samlli/Split-65/images/bottom.png

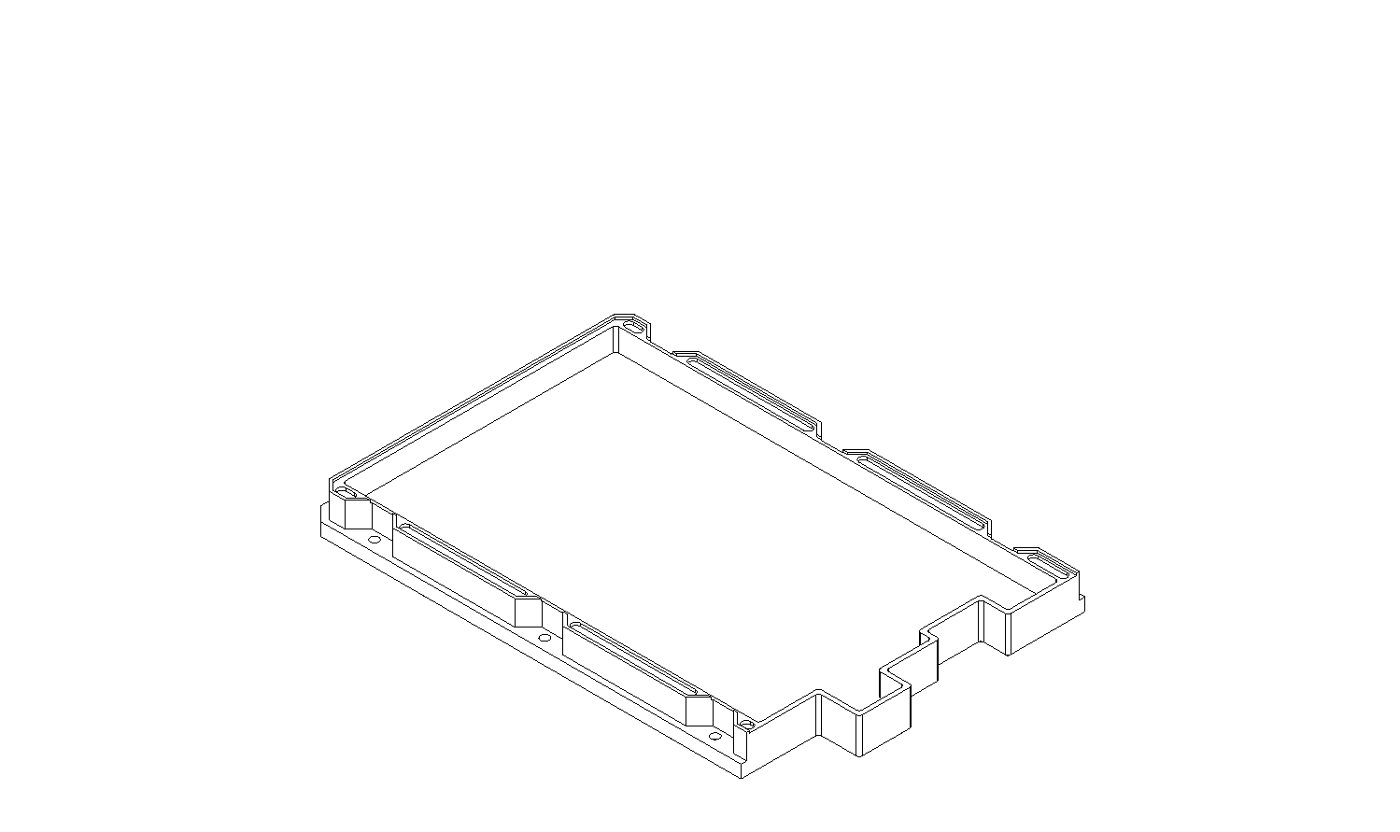
images/bottom.png
