samlli/Split-65/images/capture1.png

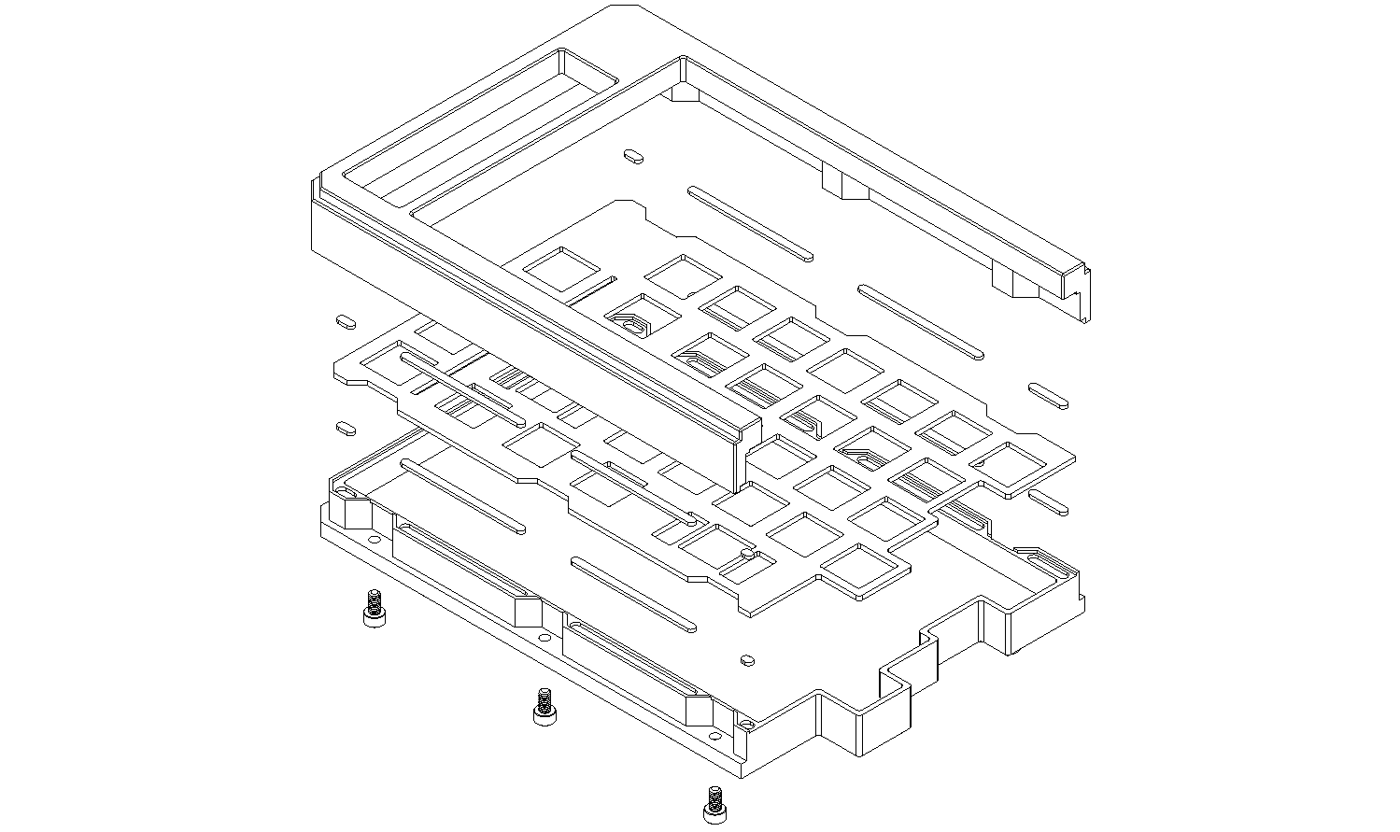
images/capture1.png
