samlli/Split-65/images/explodedview2.png

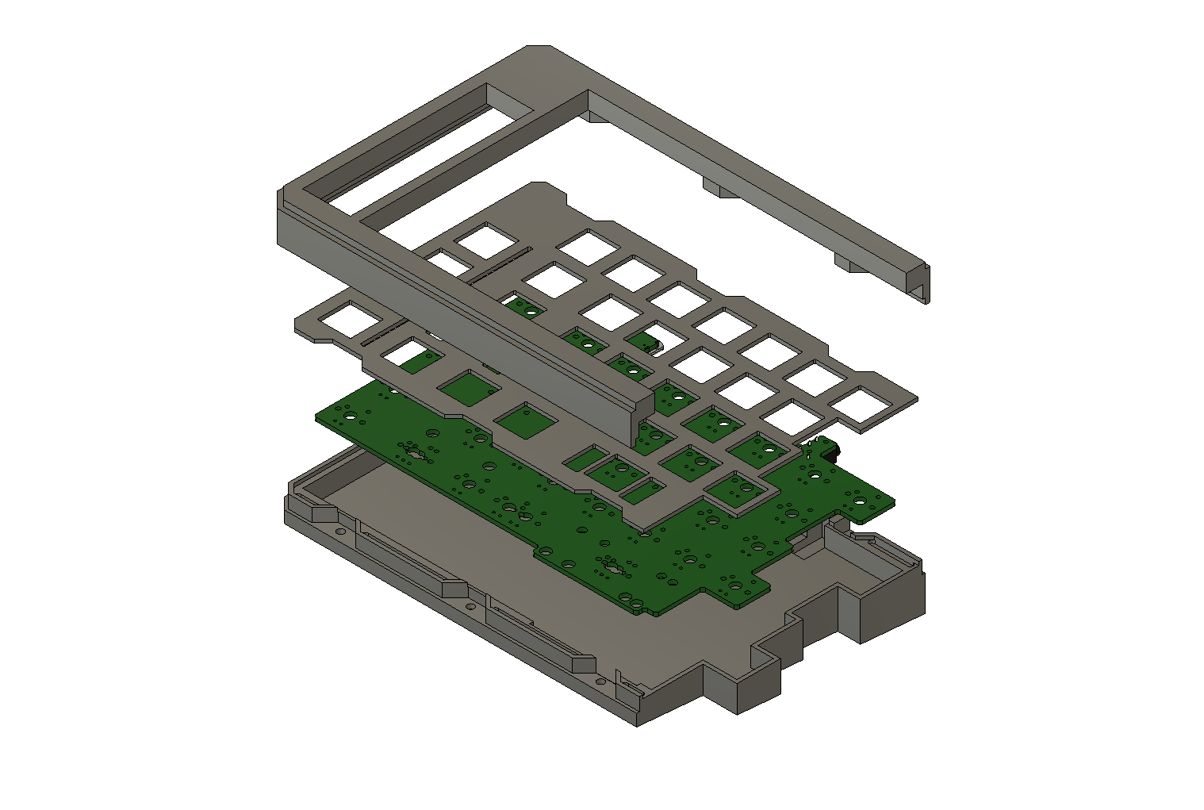
images/explodedview2.png
