samlli/Split-65/images/gasketbottom.png

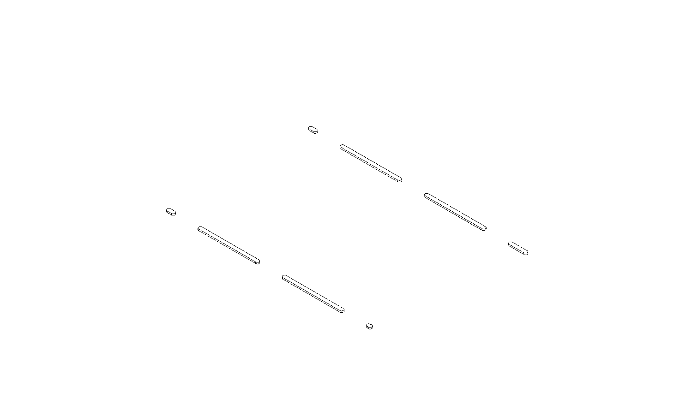
images/gasketbottom.png
