samlli/Split-65/images/gaskettop.png

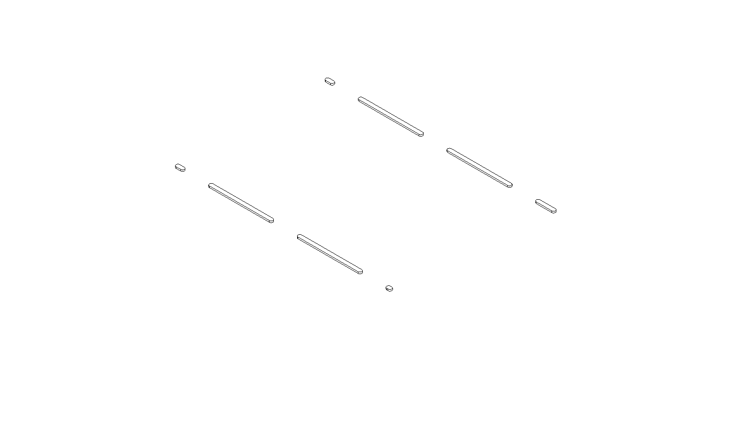
images/gaskettop.png
