samlli/Split-65/images/liverender1.png

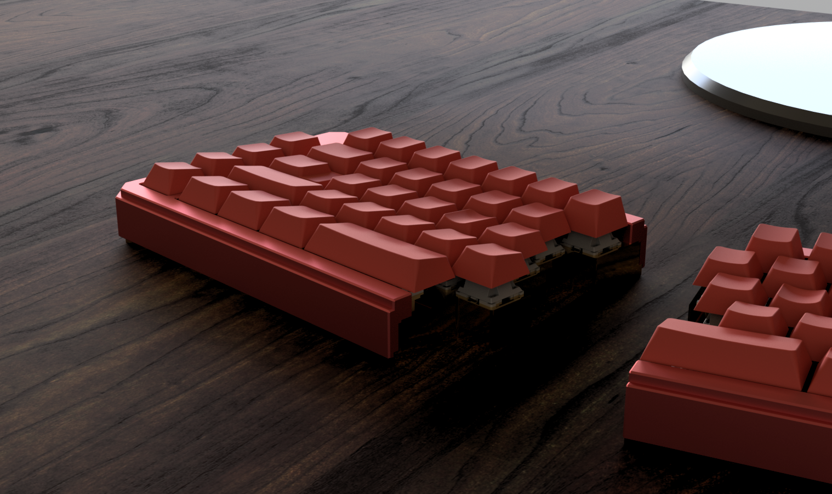
images/liverender1.png
