samlli/Split-65/images/myeyes.png

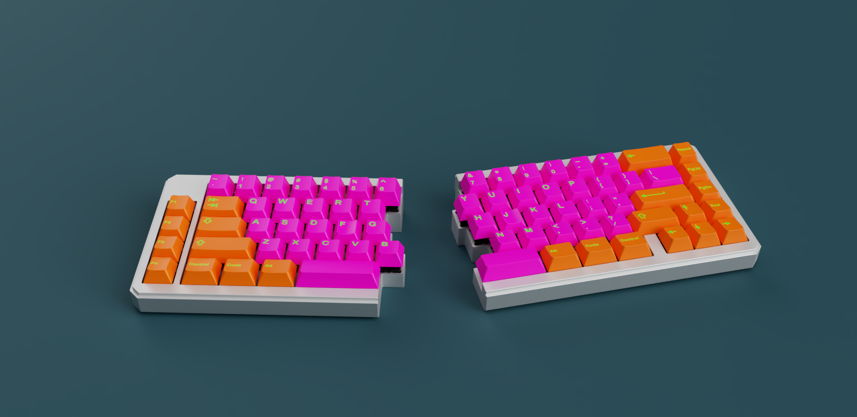
images/myeyes.png
