samlli/Split-65/images/plate.png

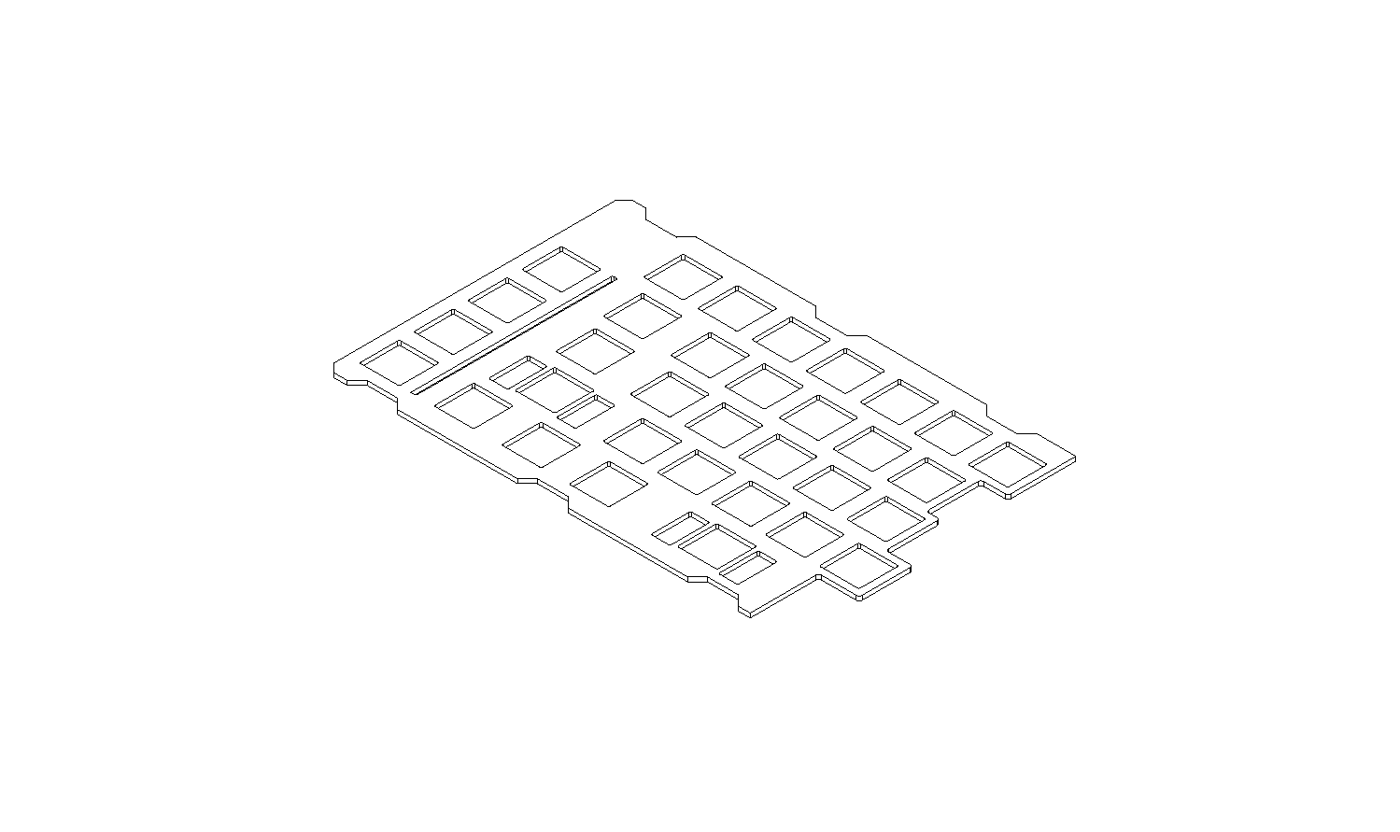
images/plate.png
