samlli/Split-65/images/render1.png

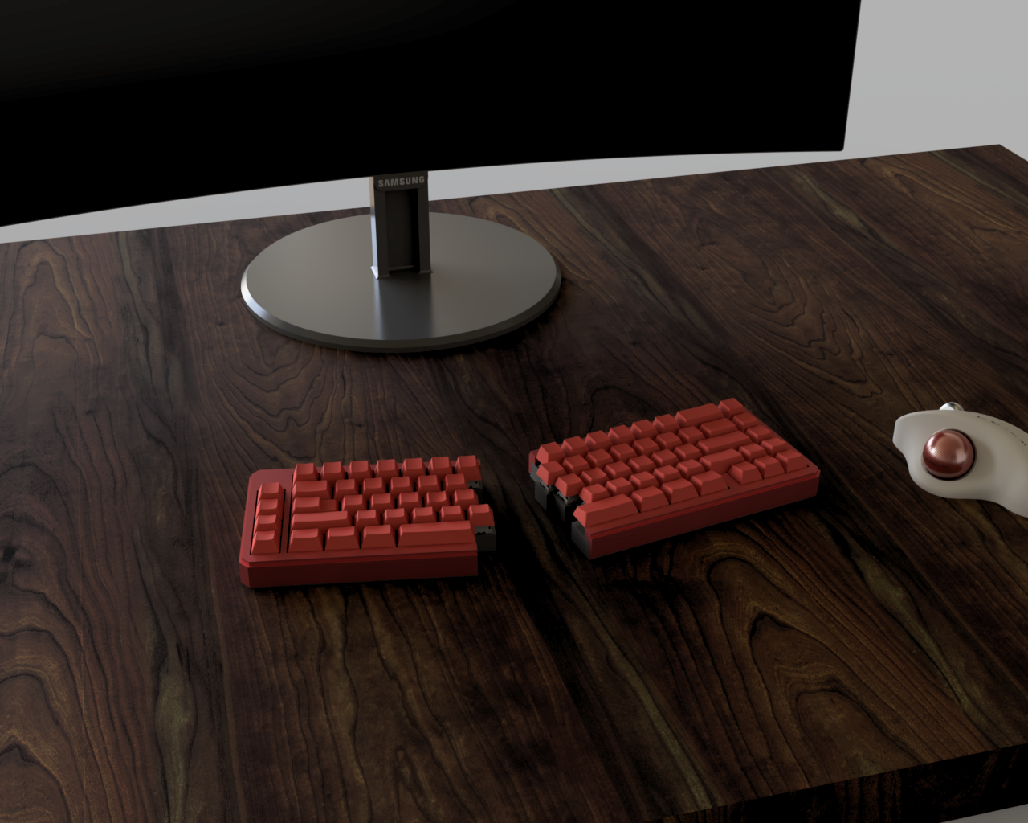
images/render1.png
