samlli/Split-65/images/render3.png

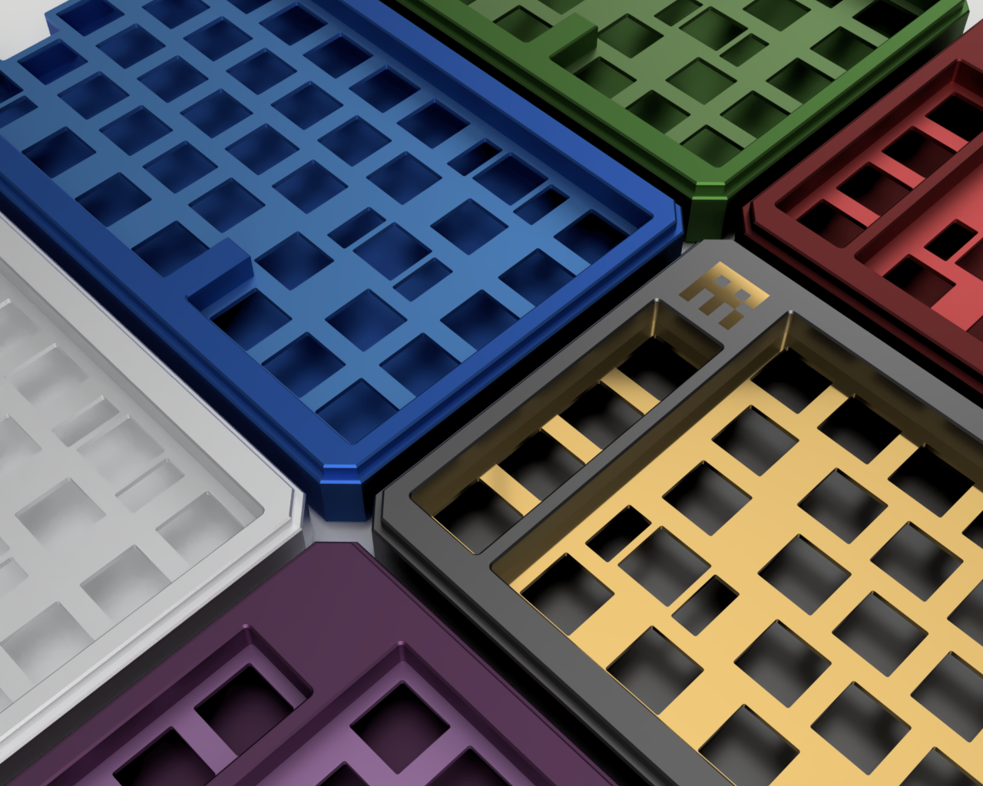
images/render3.png
