samlli/Split-65/images/screws.png

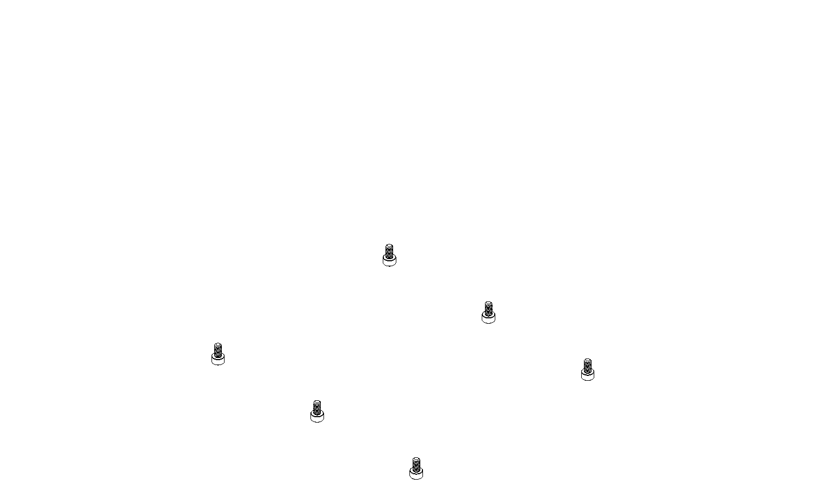
images/screws.png
