samlli/Split-65/images/ta90_blank_1.png

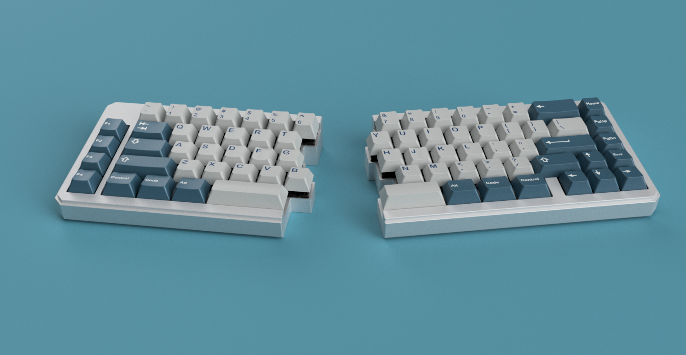
images/ta90_blank_1.png
