samlli/Split-65/images/ta90_blank_2.png

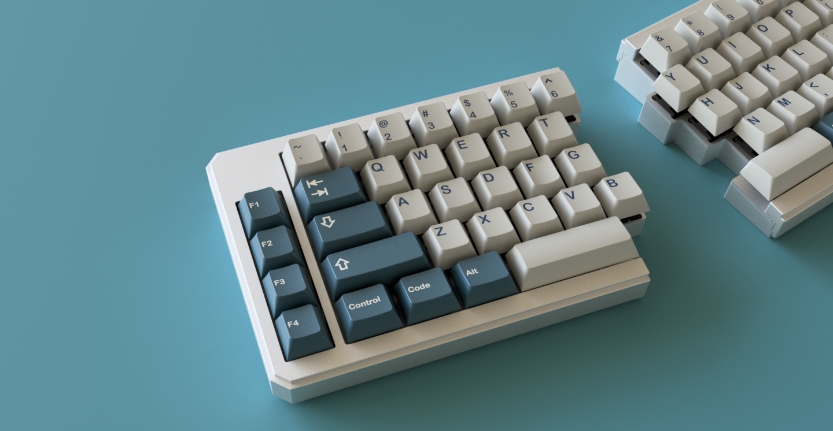
images/ta90_blank_2.png
