samlli/Split-65/images/ta90_blank_render_1.png

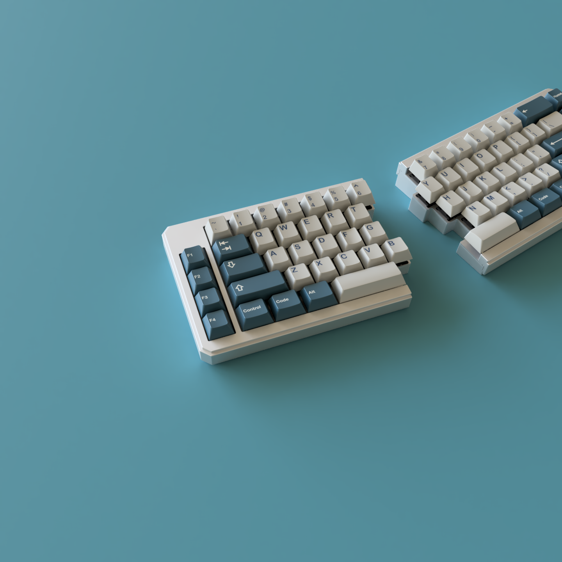
images/ta90_blank_render_1.png
