samlli/Split-65/images/ta90_render_2019-Sep-24_01-16-57AM-000_CustomizedView34420420654.png

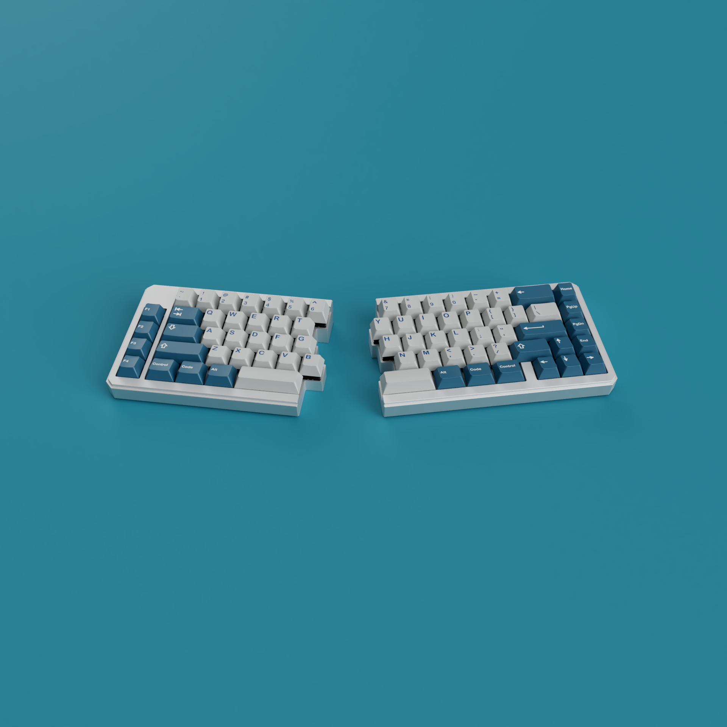
images/ta90_render_2019-Sep-24_01-16-57AM-000_CustomizedView34420420654.png
