samlli/Split-65/images/terminal_blank_render_1.png

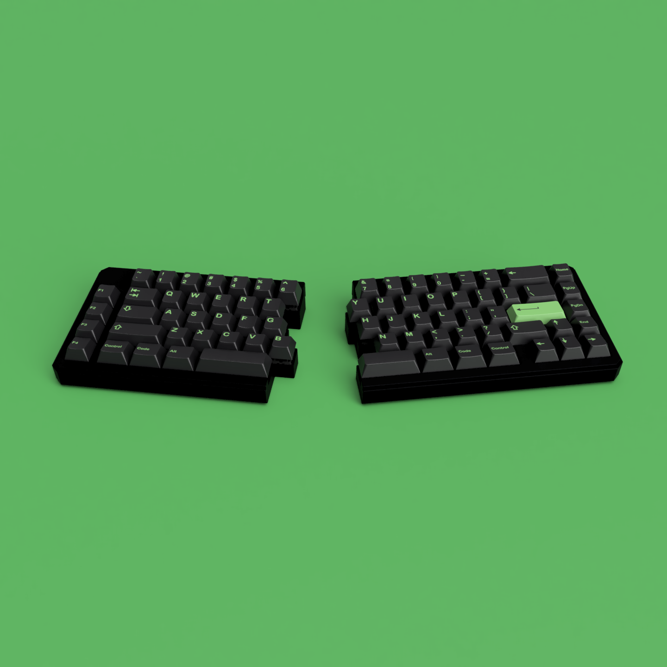
images/terminal_blank_render_1.png
