samlli/Split-65/images/terminal_blank_render_2.png

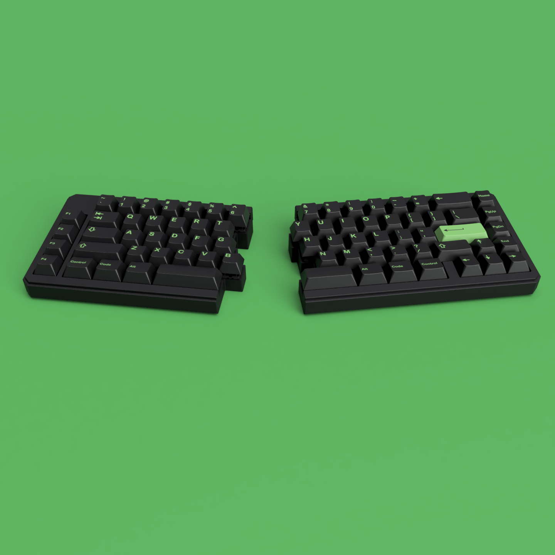
images/terminal_blank_render_2.png
