samlli/Split-65/images/top.png

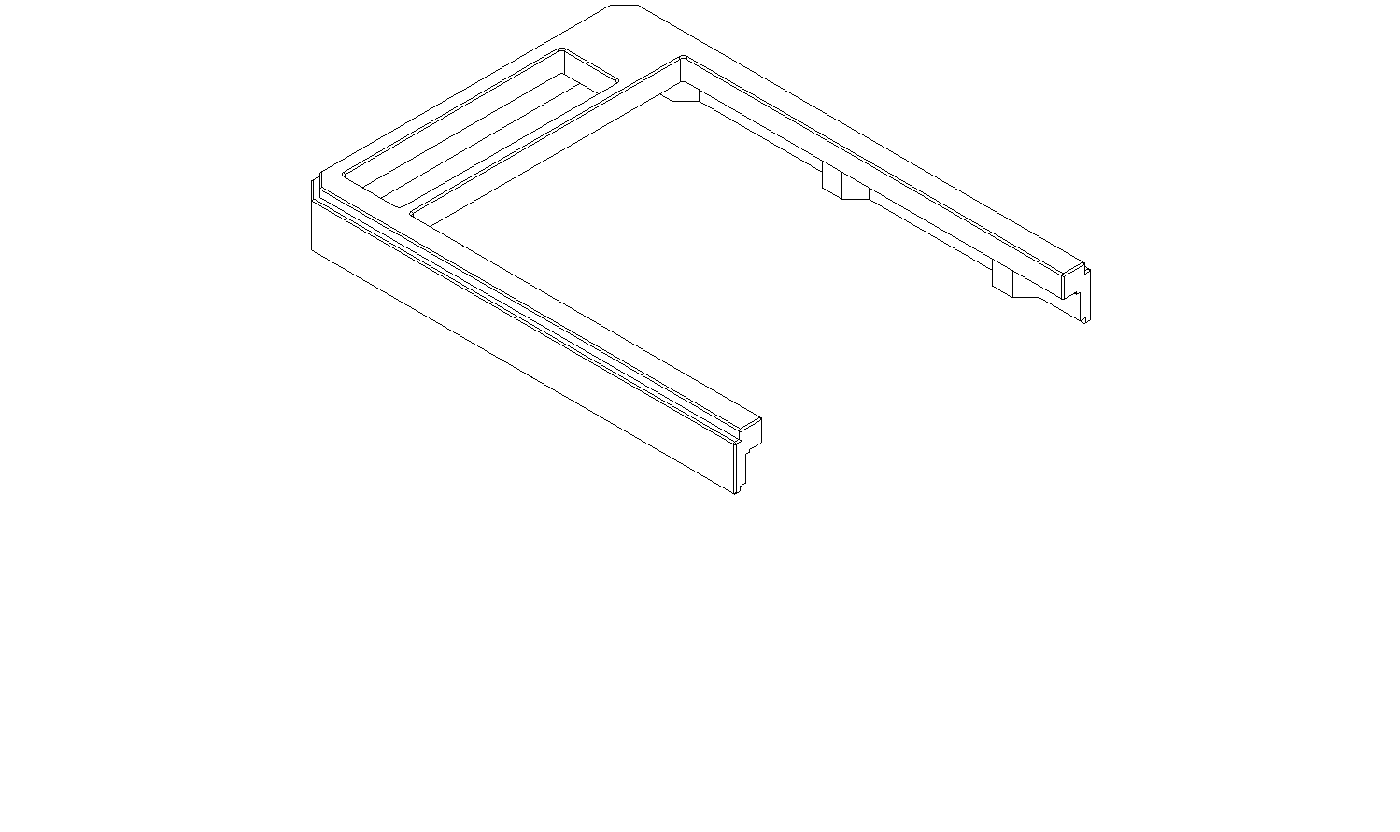
images/top.png
