samlli/Split-65/pcb/pcb_pic.png

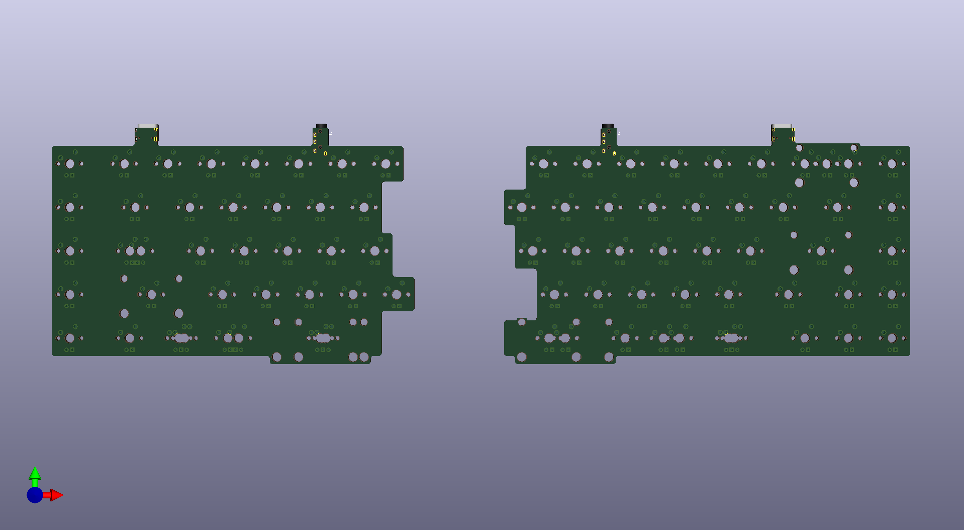
pcb/pcb_pic.png
